mariusmym/LedClock-AIO/Images/img-20241126.jpg

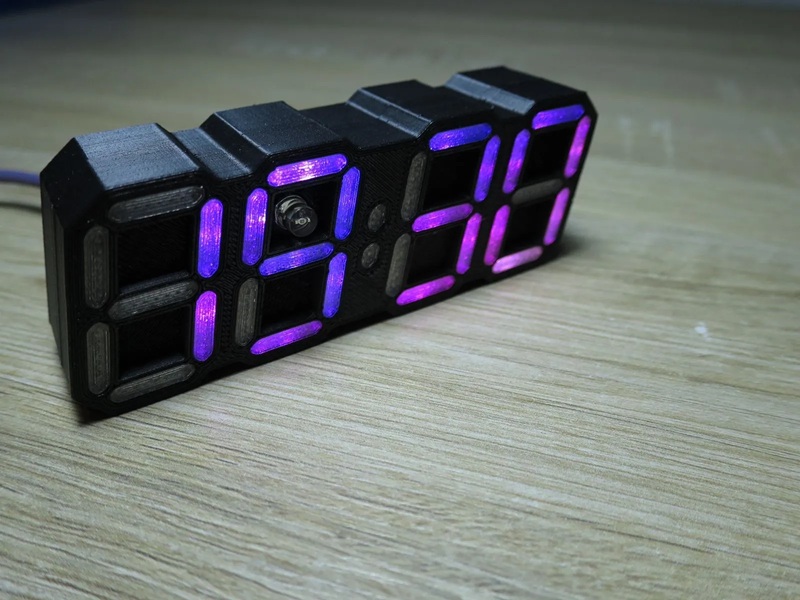
Images/img-20241126.jpg
