mariusmym/LedClock-AIO/Images/img-20241128.jpg

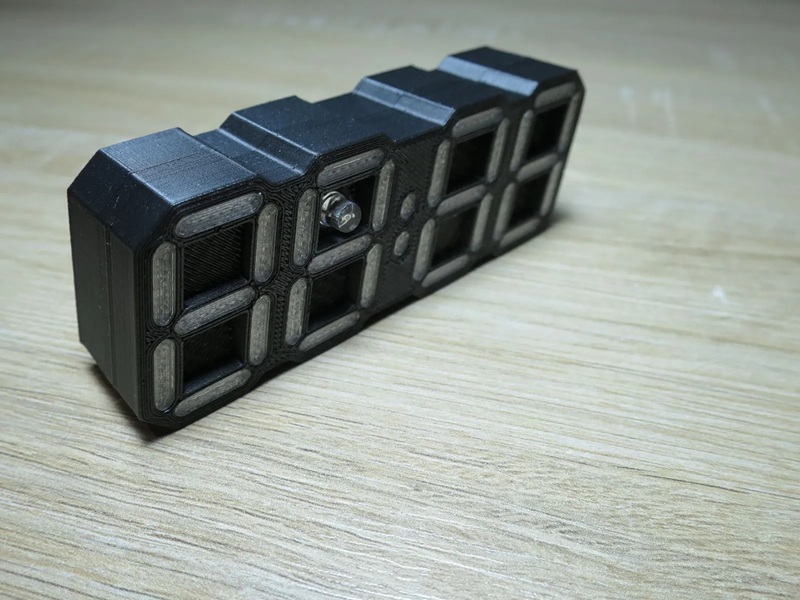
Images/img-20241128.jpg
