mariusmym/LedClock-AIO/Images/IMG_0670.JPEG

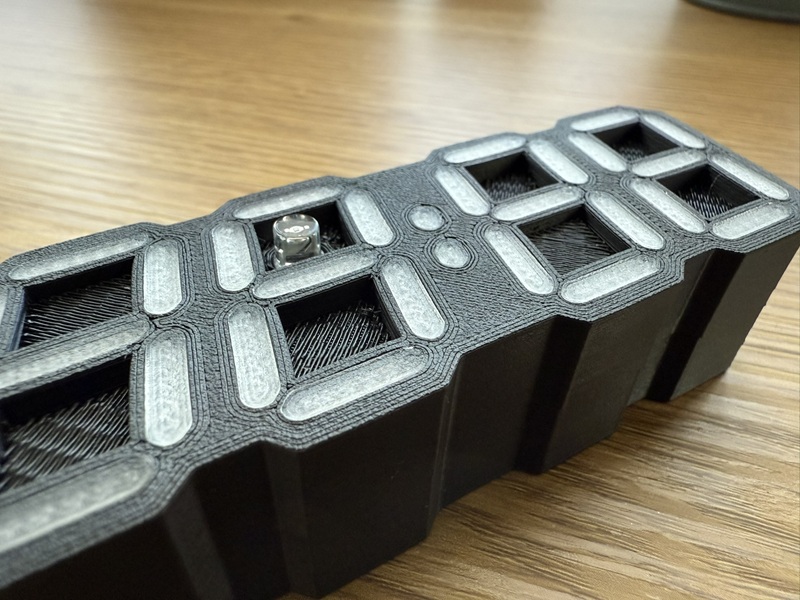
Images/IMG_0670.JPEG
