mariusmym/LedClock-AIO/Images/IMG_1792.JPEG

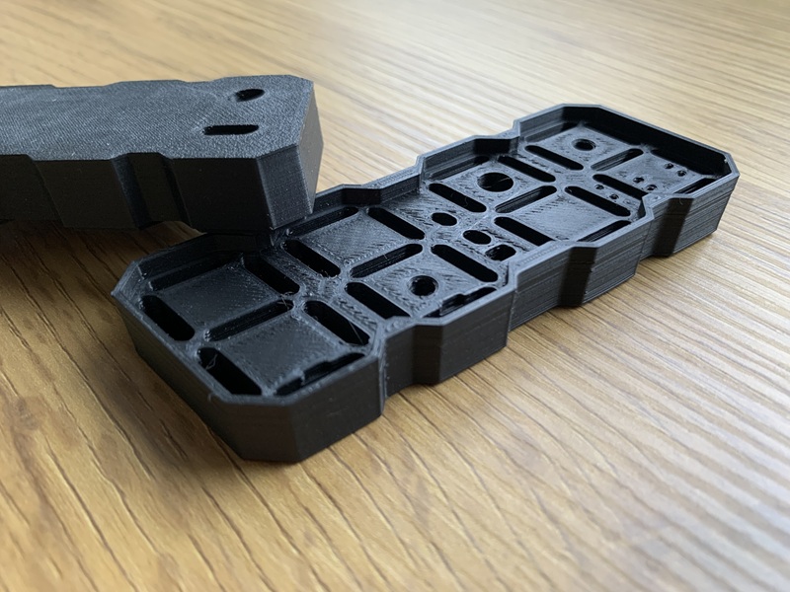
Images/IMG_1792.JPEG
