mariusmym/LedClock-AIO/Images/IMG_1823.JPEG

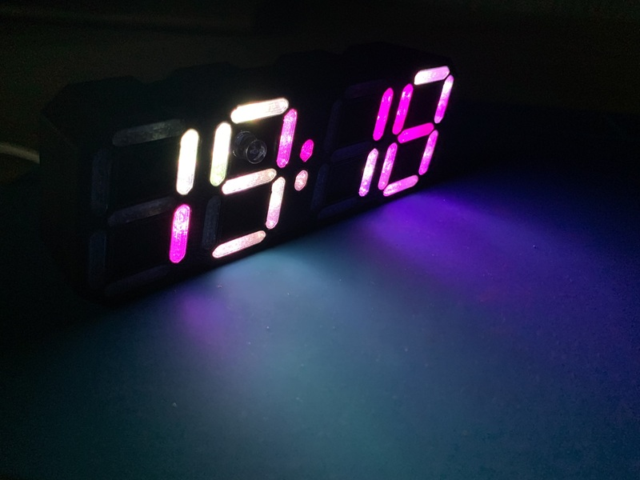
Images/IMG_1823.JPEG
