mariusmym/LedClock-AIO/Images/IMG_2306.JPEG

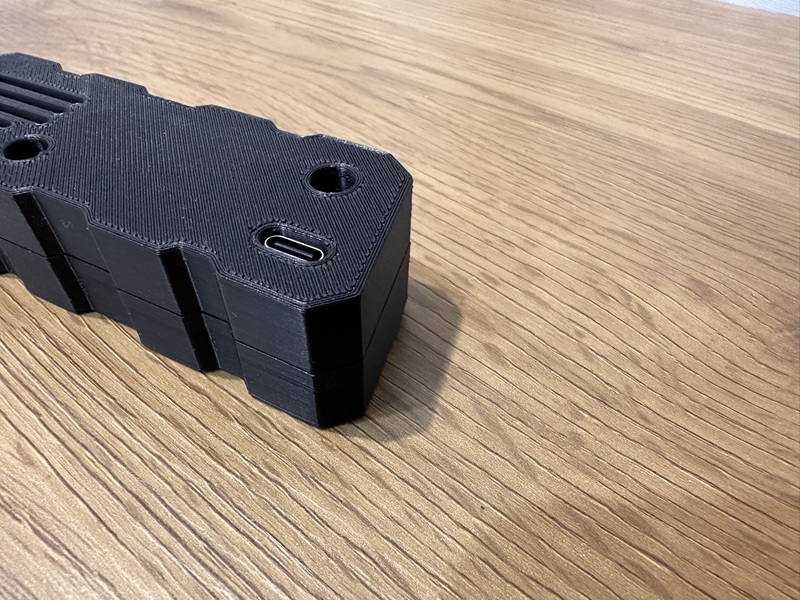
Images/IMG_2306.JPEG
