mariusmym/LedClock-AIO/Images/IMG_9273.JPEG

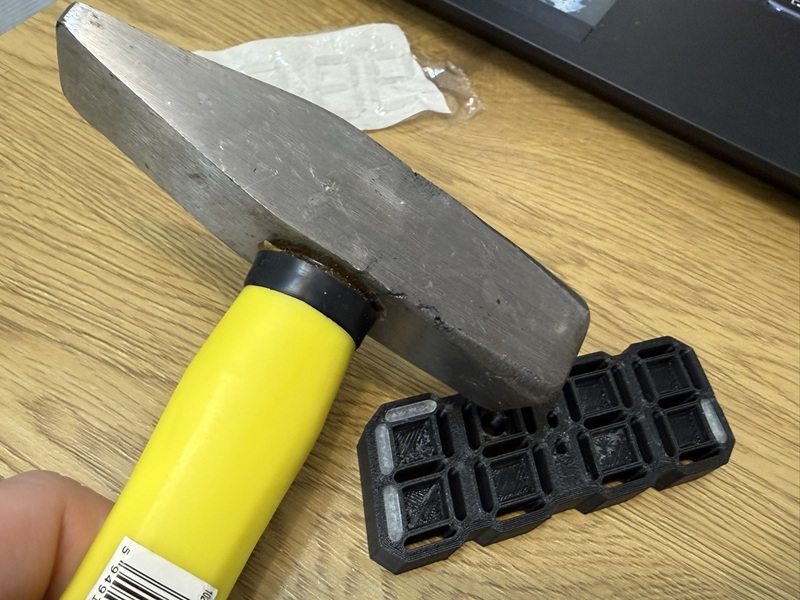
Images/IMG_9273.JPEG
