mariusmym/LedClock-AIO/Images/IMG_9386.JPEG

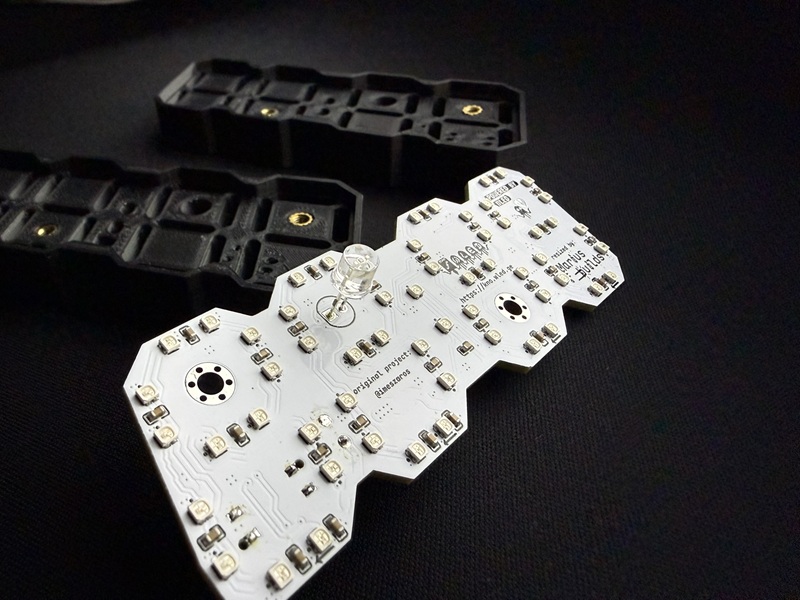
Images/IMG_9386.JPEG
