mariusmym/LedClock-AIO/Images/IMG_9396.JPEG

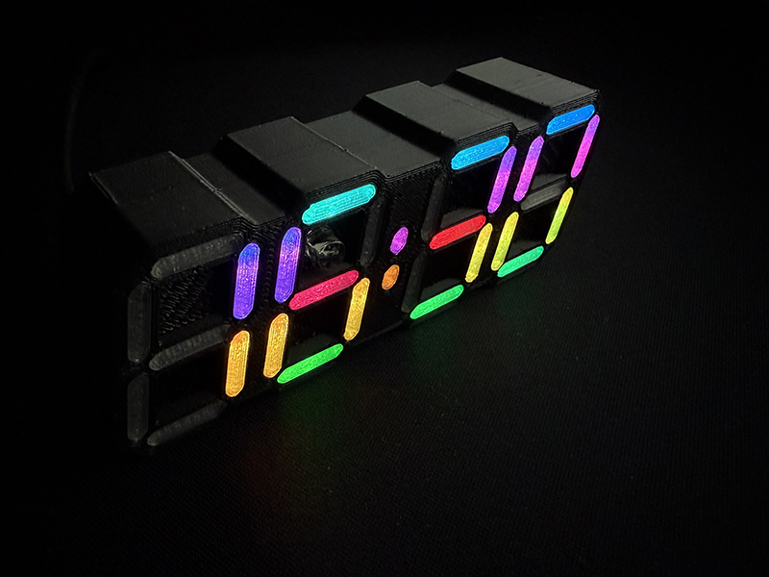
Images/IMG_9396.JPEG
